jgillick/DiscoDanceFloorV1/Construction/Exports/FloorCell.png

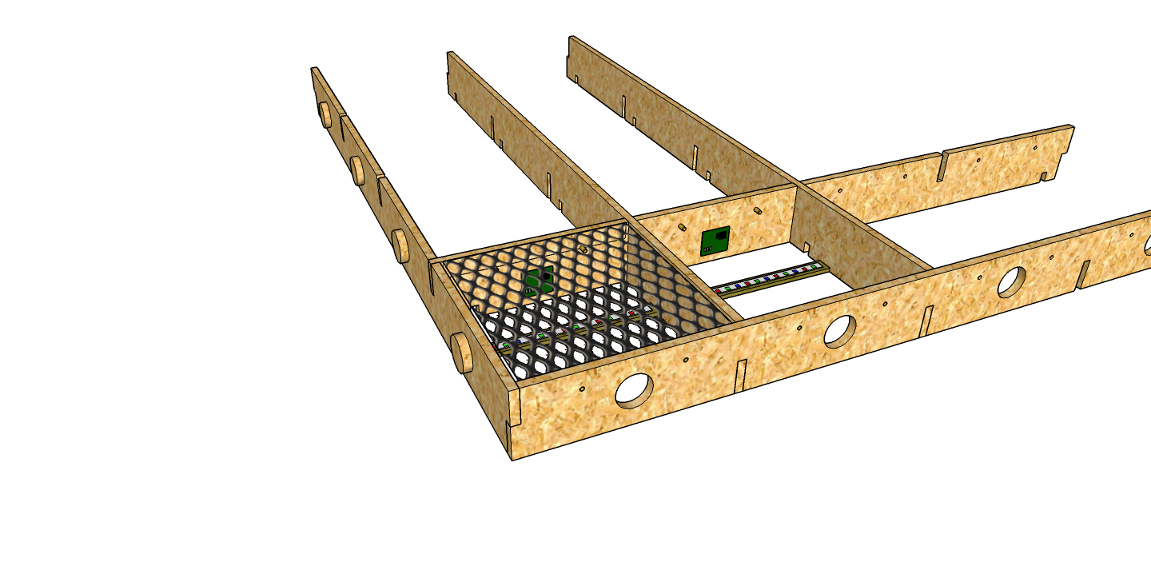
Construction/Exports/FloorCell.png
