jgillick/DiscoDanceFloorV1/Construction/Exports/FloorSection.png

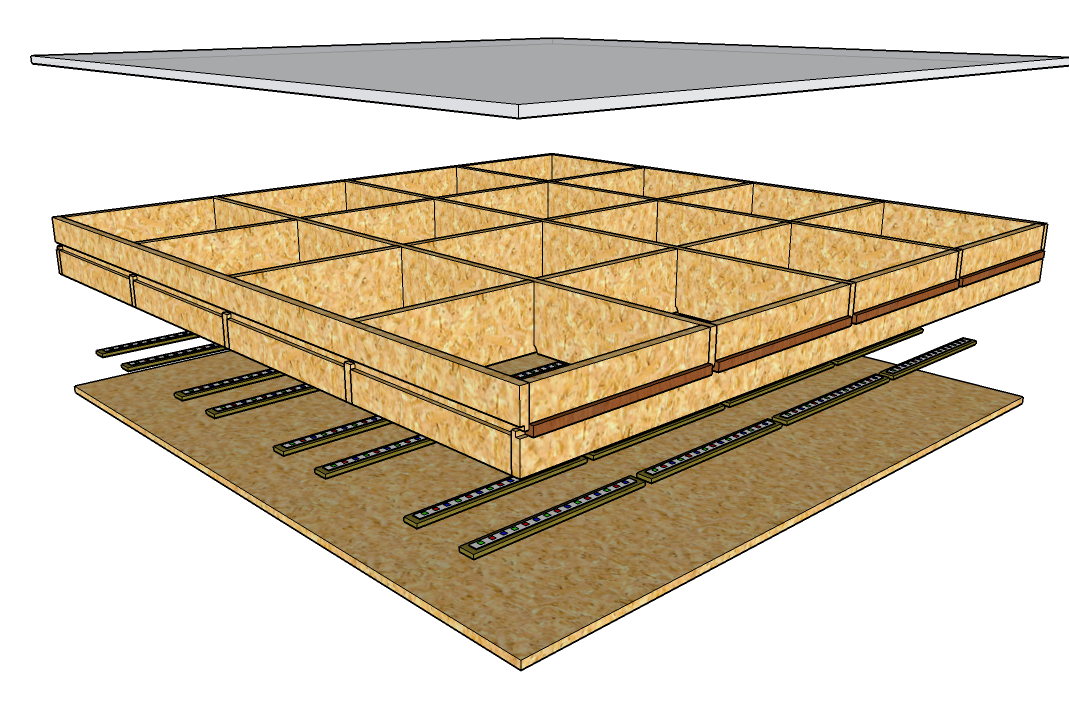
Construction/Exports/FloorSection.png
