jgillick/DiscoDanceFloorV1/Construction/Exports/RibDimensions2.png

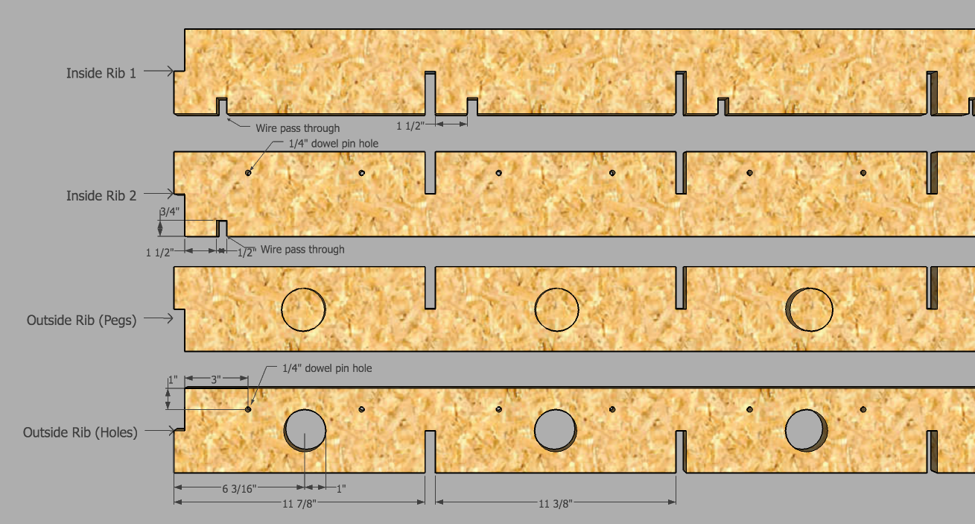
Construction/Exports/RibDimensions2.png
